marsairforce/led_breadboard_module/doc/single_high-side_active-high-or-low.png

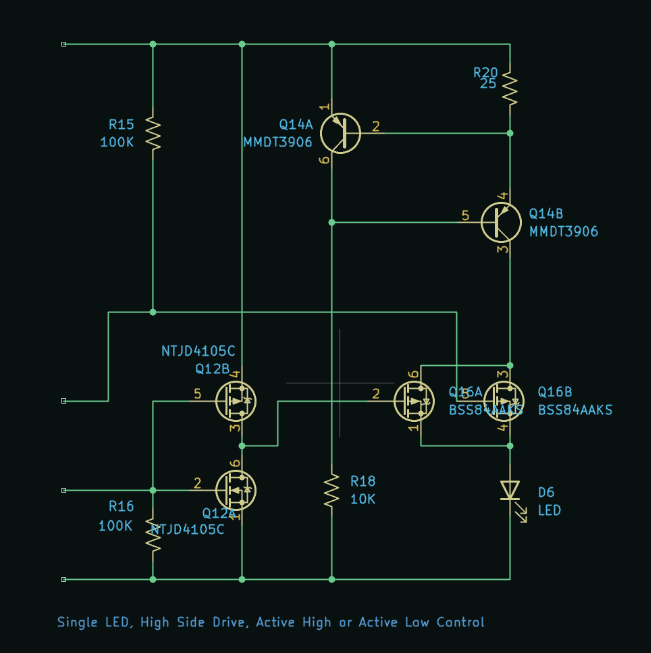
doc/single_high-side_active-high-or-low.png
